Schluggi/AIOsense/images/docs/io-i2c.jpg

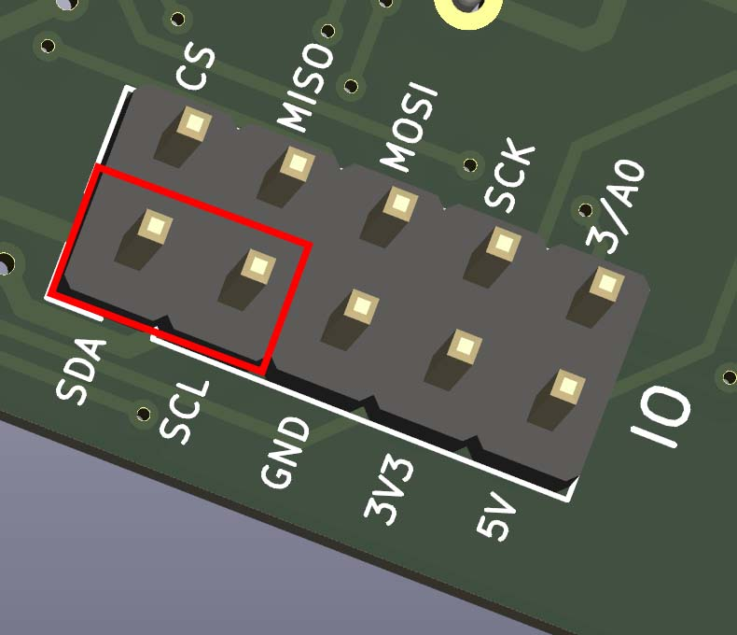
images/docs/io-i2c.jpg
